emeb/cheep3a/firmware/Sine16bit.h

#define SINE_LUT_BITS 10
/* 16-bit quarter-cycle Sine table */
const int16_t Sine16bit[ 1024 ] = {
	   25,   75,  125,  175,  226,  276,  326,  376,
	  427,  477,  527,  578,  628,  678,  728,  779,
	  829,  879,  929,  980, 1030, 1080, 1130, 1180,
	 1231, 1281, 1331, 1381, 1432, 1482, 1532, 1582,
	 1632, 1683, 1733, 1783, 1833, 1883, 1934, 1984,
	 2034, 2084, 2134, 2184, 2235, 2285, 2335, 2385,
	 2435, 2485, 2535, 2585, 2636, 2686, 2736, 2786,
	 2836, 2886, 2936, 2986, 3036, 3086, 3136, 3186,
	 3236, 3286, 3336, 3386, 3436, 3486, 3536, 3586,
	 3636, 3686, 3736, 3786, 3836, 3886, 3936, 3986,
	 4035, 4085, 4135, 4185, 4235, 4285, 4335, 4384,
	 4434, 4484, 4534, 4584, 4633, 4683, 4733, 4783,
	 4832, 4882, 4932, 4981, 5031, 5081, 5130, 5180,
	 5230, 5279, 5329, 5378, 5428, 5478, 5527, 5577,
	 5626, 5676, 5725, 5775, 5824, 5874, 5923, 5972,
	 6022, 6071, 6121, 6170, 6219, 6269, 6318, 6367,
	 6417, 6466, 6515, 6564, 6614, 6663, 6712, 6761,
	 6811, 6860, 6909, 6958, 7007, 7056, 7105, 7154,
	 7203, 7252, 7301, 7350, 7399, 7448, 7497, 7546,
	 7595, 7644, 7693, 7742, 7790, 7839, 7888, 7937,
	 7986, 8034, 8083, 8132, 8180, 8229, 8278, 8326,
	 8375, 8424, 8472, 8521, 8569, 8618, 8666, 8715,
	 8763, 8812, 8860, 8908, 8957, 9005, 9053, 9102,
	 9150, 9198, 9246, 9295, 9343, 9391, 9439, 9487,
	 9535, 9583, 9631, 9679, 9727, 9775, 9823, 9871,
	 9919, 9967,10015,10063,10111,10159,10206,10254,
	10302,10349,10397,10445,10492,10540,10588,10635,
	10683,10730,10778,10825,10873,10920,10967,11015,
	11062,11109,11157,11204,11251,11298,11345,11393,
	11440,11487,11534,11581,11628,11675,11722,11769,
	11816,11862,11909,11956,12003,12050,12096,12143,
	12190,12236,12283,12330,12376,12423,12469,12516,
	12562,12609,12655,12701,12748,12794,12840,12886,
	12933,12979,13025,13071,13117,13163,13209,13255,
	13301,13347,13393,13439,13485,13530,13576,13622,
	13667,13713,13759,13804,13850,13895,13941,13986,
	14032,14077,14123,14168,14213,14259,14304,14349,
	14394,14439,14484,14530,14575,14620,14665,14709,
	14754,14799,14844,14889,14934,14978,15023,15068,
	15112,15157,15201,15246,15290,15335,15379,15424,
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
};
