emeb/cheep3a/firmware/adc.h

/*
 * adc.h - single file header for ADC driver
 * 07-22-23 E. Brombaugh
 */
 
#ifndef __adc__
#define __adc__

/*
 * cheep3a CVs:
 * CV1 - PD4 = chl7
 * CV2 - PD3 = chl4
 * CV3 - PD2 = chl1
 */

#define ADC_NUMCHLS 3
volatile uint16_t adc_buffer[ADC_NUMCHLS];

/*
 * initialize adc for DMA
 */
void adc_init( void )
{
	// ADCCLK = 24 MHz => RCC_ADCPRE = 0: divide by 2
	RCC->CFGR0 &= ~(0x1F<<11);
	
	// Enable GPIOD and ADC
	RCC->APB2PCENR |=	RCC_APB2Periph_GPIOD | RCC_APB2Periph_ADC1;
	
	// PD4 is analog input chl 7
	GPIOD->CFGLR &= ~(0xf<<(4*4));	// CNF = 00: Analog, MODE = 00: Input
	
	// PD3 is analog input chl 4
	GPIOD->CFGLR &= ~(0xf<<(4*3));	// CNF = 00: Analog, MODE = 00: Input
	
	// PD2 is analog input chl 3
	GPIOD->CFGLR &= ~(0xf<<(4*2));	// CNF = 00: Analog, MODE = 00: Input
	
	// Reset the ADC to init all regs
	RCC->APB2PRSTR |= RCC_APB2Periph_ADC1;
	RCC->APB2PRSTR &= ~RCC_APB2Periph_ADC1;
	
	// Set up four conversions on chl 7, 4, 3
	ADC1->RSQR1 = (ADC_NUMCHLS-1) << 20;	// four chls in the sequence
	ADC1->RSQR2 = 0;
	ADC1->RSQR3 = (7<<(5*0)) | (4<<(5*1)) | (3<<(5*2));
	
	// set sampling time for chl 7, 4, 3
	// 0:7 => 3/9/15/30/43/57/73/241 cycles
	ADC1->SAMPTR2 = (7<<(3*7)) | (7<<(3*4)) | (7<<(3*3));

	// turn on ADC
	ADC1->CTLR2 |= ADC_ADON;
	
	// Reset calibration
	ADC1->CTLR2 |= ADC_RSTCAL;
	while(ADC1->CTLR2 & ADC_RSTCAL);
	
	// Calibrate
	ADC1->CTLR2 |= ADC_CAL;
	while(ADC1->CTLR2 & ADC_CAL);
	
	// Turn on DMA
	RCC->AHBPCENR |= RCC_AHBPeriph_DMA1;
	
	//DMA1_Channel1 is for ADC
	DMA1_Channel1->PADDR = (uint32_t)&ADC1->RDATAR;
	DMA1_Channel1->MADDR = (uint32_t)adc_buffer;
	DMA1_Channel1->CNTR  = ADC_NUMCHLS;
	DMA1_Channel1->CFGR  =
		DMA_M2M_Disable |		 
		DMA_Priority_VeryHigh |
		DMA_MemoryDataSize_HalfWord |
		DMA_PeripheralDataSize_HalfWord |
		DMA_MemoryInc_Enable |
		DMA_Mode_Circular |
		DMA_DIR_PeripheralSRC;
	
	// Turn on DMA channel 1
	DMA1_Channel1->CFGR |= DMA_CFGR1_EN;
	
	// enable scanning
	ADC1->CTLR1 |= ADC_SCAN;
	
	// Enable continuous conversion and DMA
	ADC1->CTLR2 |= ADC_CONT | ADC_DMA | ADC_EXTSEL;
	
	// start conversion
	ADC1->CTLR2 |= ADC_SWSTART;
}


#endif
