emeb/cheep3a/firmware/funconfig.h

#ifndef _FUNCONFIG_H
#define _FUNCONFIG_H

#define FUNCONF_SYSTICK_USE_HCLK 1
#define FUNCONF_USE_HSE 1               // Use External Oscillator
//#define FUNCONF_USE_UARTPRINTF  0

#define CH32V003        1

#endif
